keyzog/kapl/images/case/acrylic/bottom_withLeds.jpg

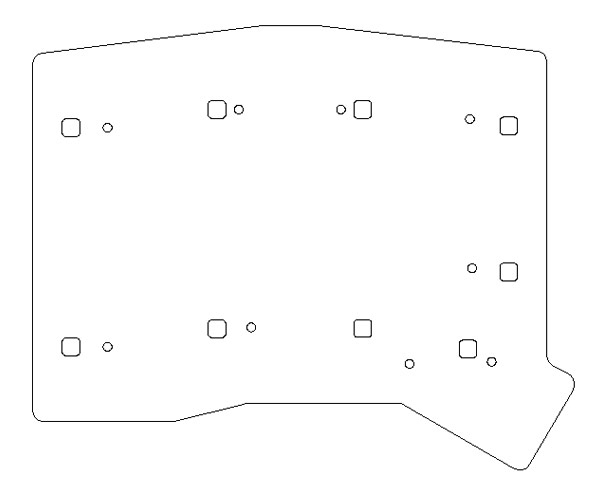
images/case/acrylic/bottom_withLeds.jpg
