keyzog/kapl/images/case/pcb/bottom_withLeds_withMKcut.jpg

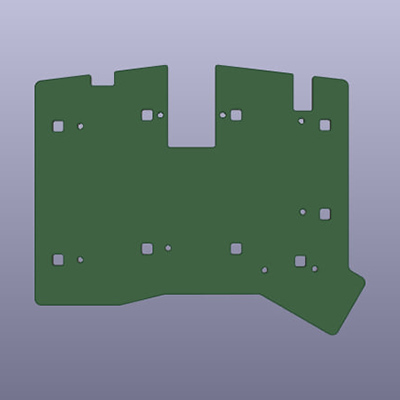
images/case/pcb/bottom_withLeds_withMKcut.jpg
