keyzog/kapl/images/case_base.jpg

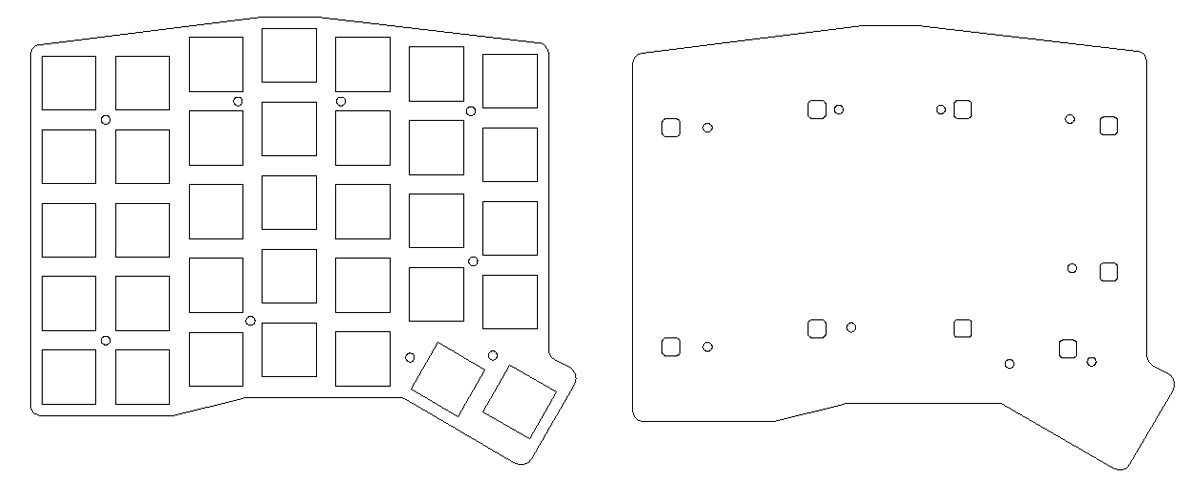
images/case_base.jpg
