keyzog/kapl/images/leds_pin.png

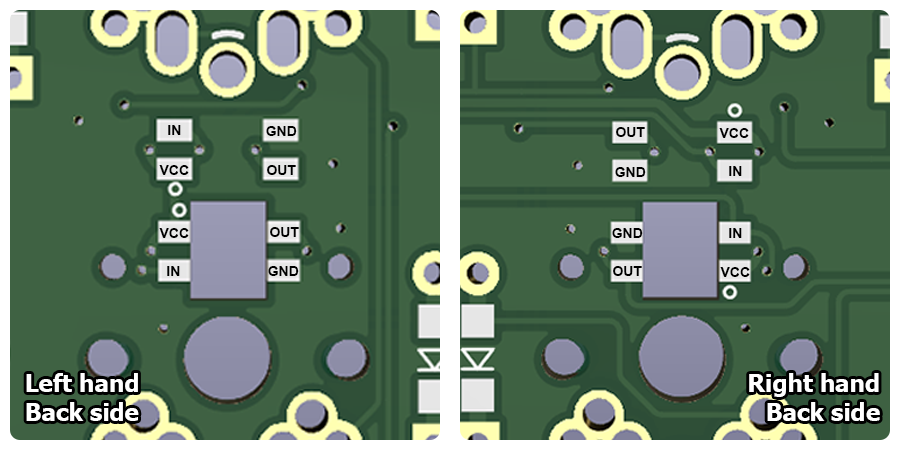
images/leds_pin.png
