keyzog/kapl/images/leds_strip.jpg

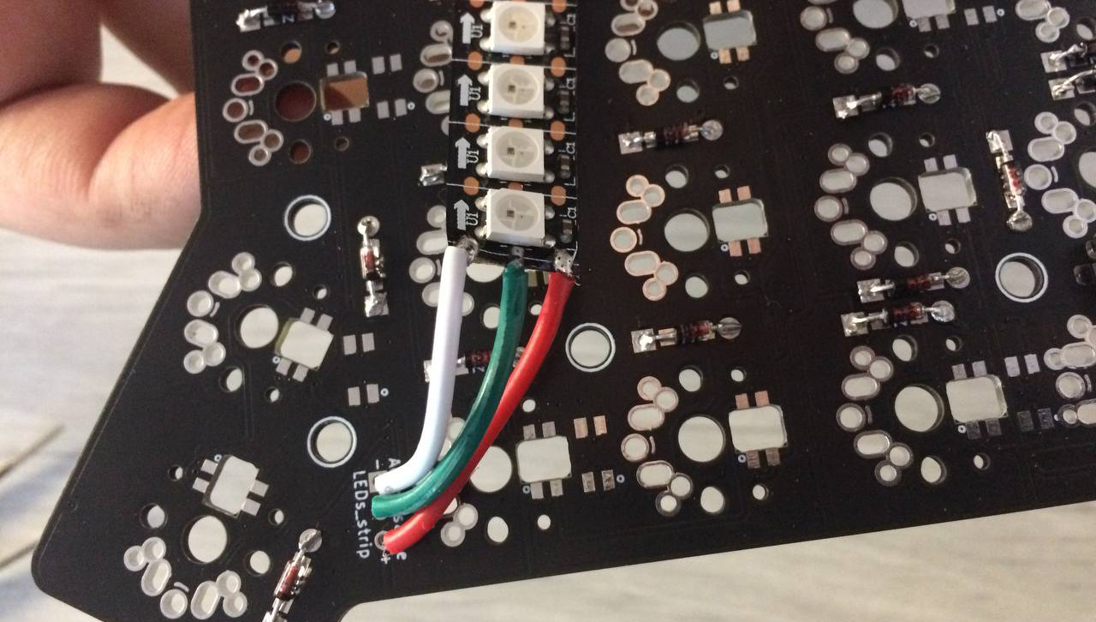
images/leds_strip.jpg
